uttam-vishnumahanthi/multi-output-dc-dc-buck-converter/hardware/hardware images/1.jpeg

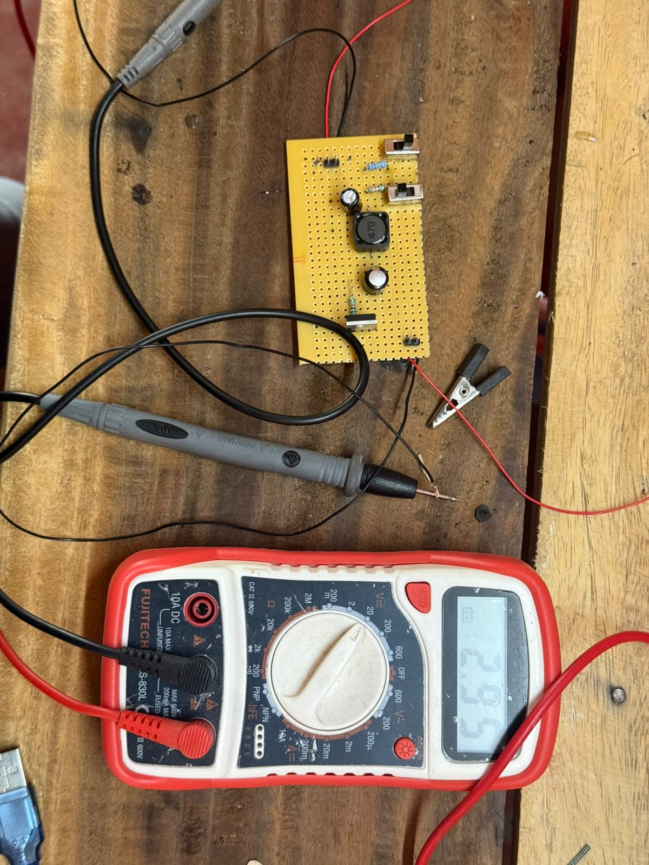
hardware/hardware images/1.jpeg
