uttam-vishnumahanthi/multi-output-dc-dc-buck-converter/hardware/hardware images/2.jpeg

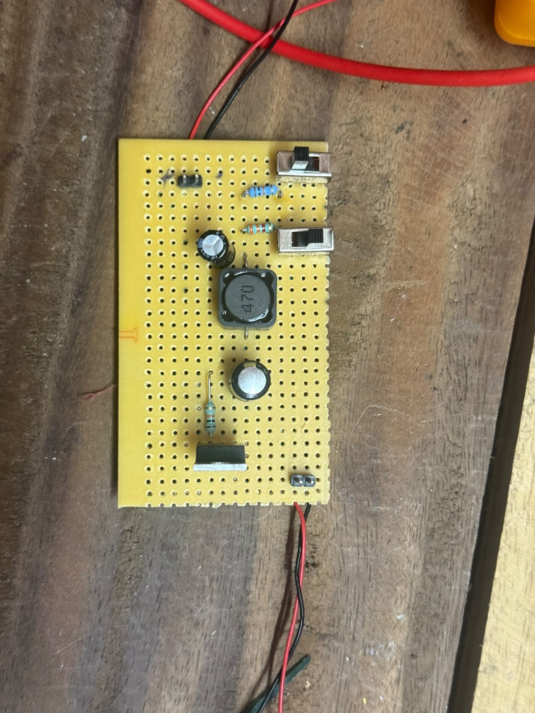
hardware/hardware images/2.jpeg
