uttam-vishnumahanthi/multi-output-dc-dc-buck-converter/images/2596.png

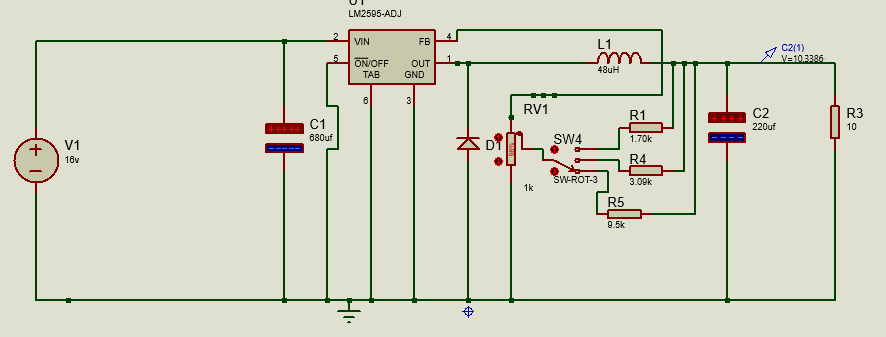
images/2596.png
